Stan6314/TinyBasRO/src/charstable.h

// Table with BASIC commands - every command is in 8 Bytes
// First byte is lenght of command, including space at the end
// Then ASCII characters of command name + closing space
const uint8_t KeyWordTab[] = {
0x06,0x50,0x52,0x49,0x4E,0x54,0x20,0x00,	// PRINT - 0xA0
0x03,0x49,0x46,0x20,0x00,0x00,0x00,0x00,	// IF - 0xA1
0x05,0x54,0x48,0x45,0x4E,0x20,0x00,0x00,	// THEN - 0xA2
0x05,0x47,0x4F,0x54,0x4F,0x20,0x00,0x00,	// GOTO - 0xA3
0x06,0x49,0x4E,0x50,0x55,0x54,0x20,0x00,	// INPUT - 0xA4
0x04,0x4C,0x45,0x54,0x20,0x00,0x00,0x00,	// LET - 0xA5
0x06,0x47,0x4F,0x53,0x55,0x42,0x20,0x00,	// GOSUB - 0xA6
0x07,0x52,0x45,0x54,0x55,0x52,0x4E,0x20,	// RETURN - 0xA7
0x06,0x43,0x4C,0x45,0x41,0x52,0x20,0x00,	// CLEAR - 0xA8
0x05,0x4C,0x49,0x53,0x54,0x20,0x00,0x00,	// LIST - 0xA9
0x04,0x52,0x55,0x4E,0x20,0x00,0x00,0x00,	// RUN - 0xAA
0x04,0x45,0x4E,0x44,0x20,0x00,0x00,0x00,	// END - 0xAB

0x05,0x54,0x49,0x4D,0x45,0x20,0x00,0x00,	// TIME - 0xAC
0x07,0x43,0x55,0x52,0x53,0x4F,0x52,0x20,	// CURSOR - 0xAD
0x06,0x50,0x55,0x54,0x43,0x48,0x20,0x00,	// PUTCH - 0xAE
0x06,0x47,0x45,0x54,0x43,0x48,0x20,0x00,	// GETCH - 0xAF
0x06,0x49,0x4E,0x4B,0x45,0x59,0x20,0x00,	// INKEY - 0xB0
0x05,0x46,0x49,0x4C,0x45,0x20,0x00,0x00,	// FILE - 0xB1
0x05,0x44,0x49,0x53,0x4B,0x20,0x00,0x00,	// DISK - 0xB2
0x06,0x44,0x45,0x4C,0x41,0x59,0x20,0x00,	// DELAY - 0xB3
0x05,0x42,0x45,0x45,0x50,0x20,0x00,0x00,	// BEEP - 0xB4
0x04,0x52,0x45,0x4D,0x20,0x00,0x00,0x00, 	// REM - 0xB5

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
  0x00, 0x00, 0x03, 0x07, 0x0C, 0x18,// Gr26
  0x18, 0x0C, 0x07, 0x03, 0x00, 0x00,// Gr27
  0x00, 0x00, 0xFF, 0xFF, 0x00, 0x00,// Gr28
  0x18, 0x18, 0x18, 0x18, 0x18, 0x18,// Gr29
  0x18, 0x18, 0xFF, 0xFF, 0x18, 0x18,// Gr30
  0x55, 0xAA, 0x55, 0xAA, 0x55, 0xAA // Gr31 
};
